TheElesty/electronic-chess/manufacturing/printing/raw/pieces/knight.stl

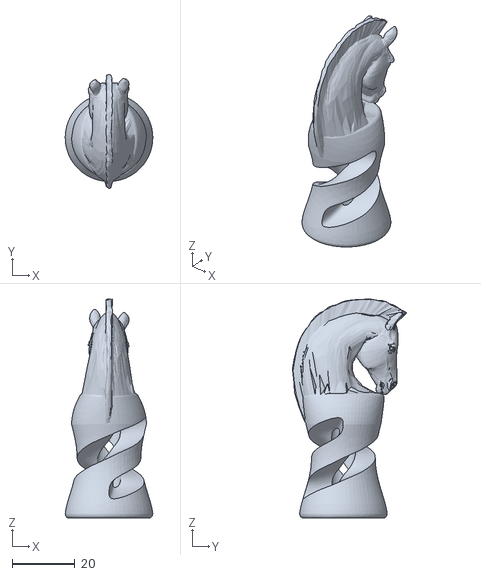
[picture p15: CAD file, 2024-05-08]
manufacturing/printing/raw/pieces/knight.stl
28.0 x 36.5 x 70.0
