TheElesty/electronic-chess/board_model/MODELS/Assets/_RFID-RC522.cd1ec80f-b667-4655-b6b3-a21b5d1b7a74 v7.3mf

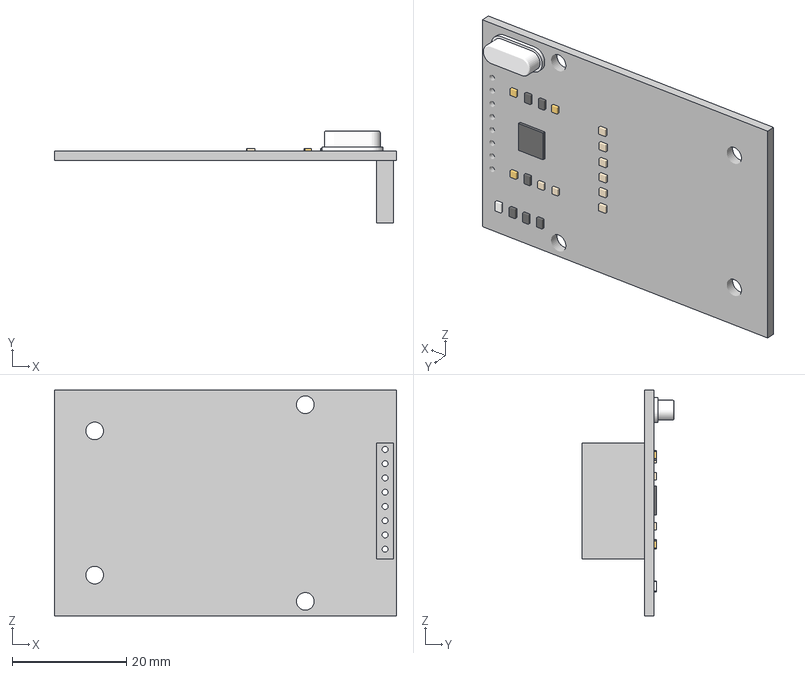
[picture p16: CAD file, 2024-05-08]
board_model/MODELS/Assets/_RFID-RC522.cd1ec80f-b667-4655-b6b3-a21b5d1b7a74 v7.3mf
60.0 x 16.1 x 39.6 mm
Clock
base
