TheElesty/electronic-chess/manufacturing/laser_cut/raw/top_board.dxf

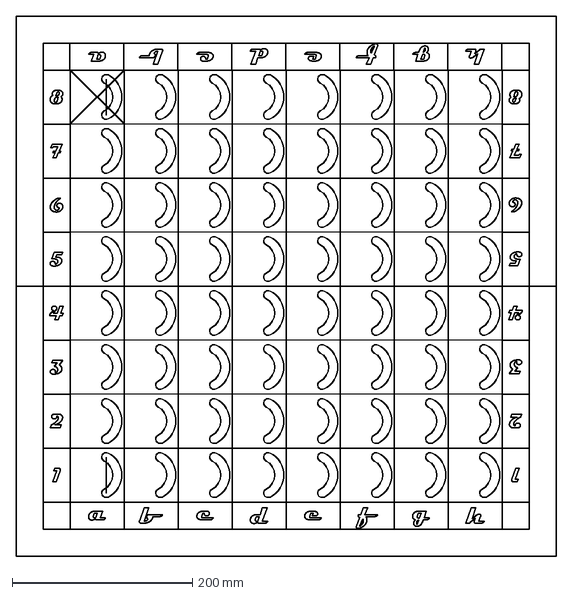
[picture p17: CAD file, 2024-05-08]
manufacturing/laser_cut/raw/top_board.dxf
600.0 x 600.0 mm
