TheElesty/electronic-chess/manufacturing/printing/chess_board_mx_holders.3mf

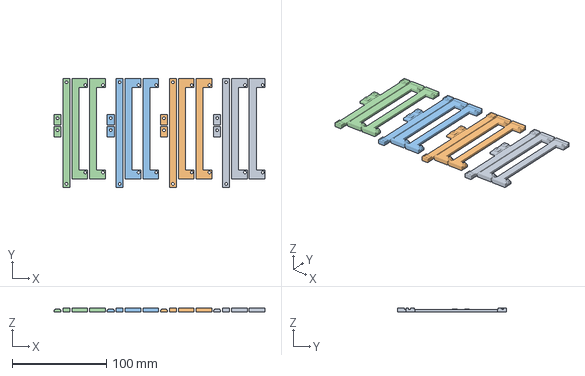
[picture p18: CAD file, 2024-05-08]
manufacturing/printing/chess_board_mx_holders.3mf
224.0 x 115.3 x 4.50 mm
Assembly x 4
