TheElesty/electronic-chess/manufacturing/printing/raw/pieces/rook.stl

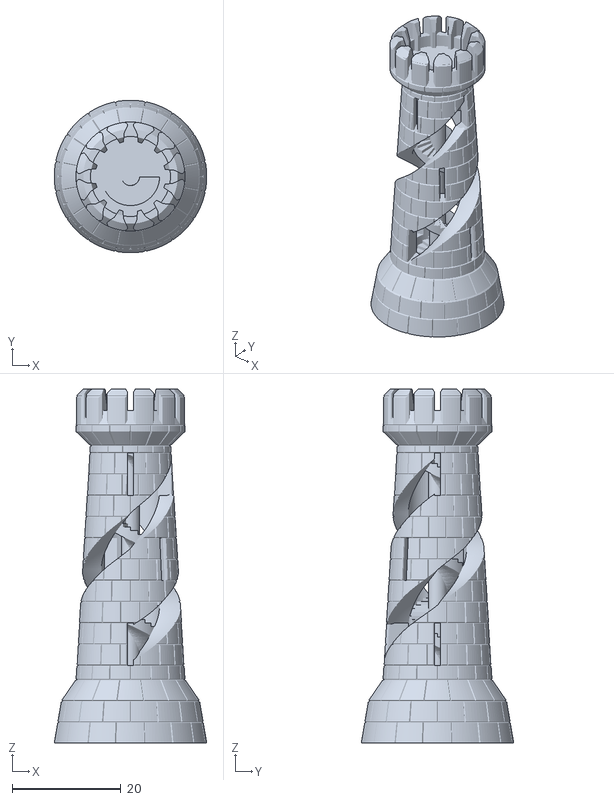
[picture p19: CAD file, 2024-05-08]
manufacturing/printing/raw/pieces/rook.stl
28.0 x 28.0 x 65.0
