TheElesty/electronic-chess/manufacturing/printing/raw/SUPPORTED_light_tunnel.stl

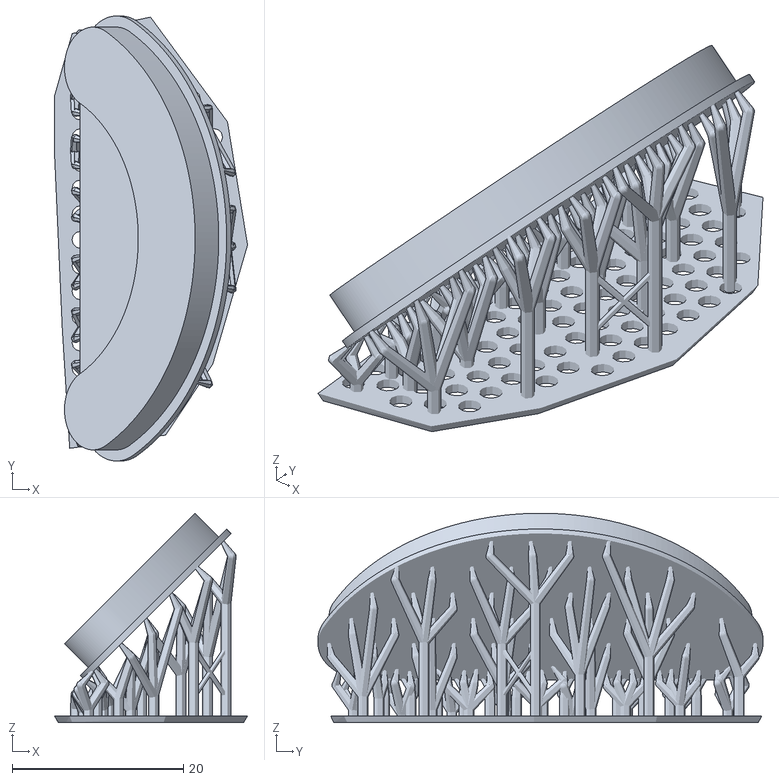
[picture p20: CAD file, 2024-05-08]
manufacturing/printing/raw/SUPPORTED_light_tunnel.stl
22.6 x 52.0 x 24.5
