TheElesty/electronic-chess/manufacturing/laser_cut/raw/short_side.dxf

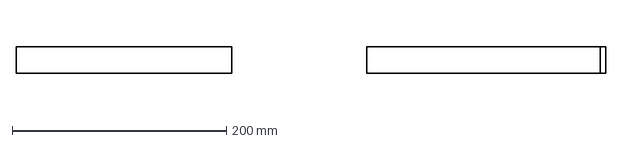
[picture p21: CAD file, 2024-05-08]
manufacturing/laser_cut/raw/short_side.dxf
550.0 x 25.0 mm
