TheElesty/electronic-chess/manufacturing/printing/led_support_2x.3mf

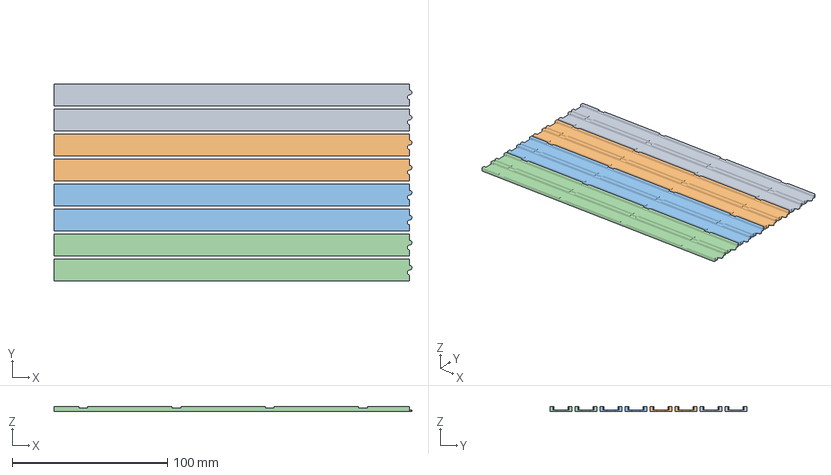
[picture p22: CAD file, 2024-05-08]
manufacturing/printing/led_support_2x.3mf
230.3 x 126.8 x 3.00 mm
Assembly x 4
