TheElesty/electronic-chess/manufacturing/printing/raw/chess_board_mx_holder.stl

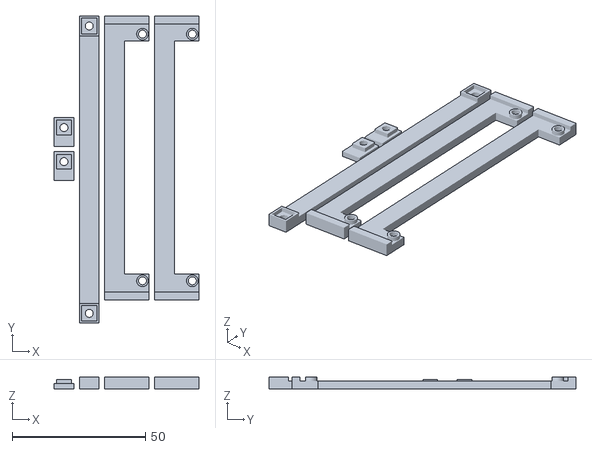
[picture p23: CAD file, 2024-05-08]
manufacturing/printing/raw/chess_board_mx_holder.stl
54.5 x 115.3 x 4.50
