TheElesty/electronic-chess/manufacturing/printing/raw/pieces/king.stl

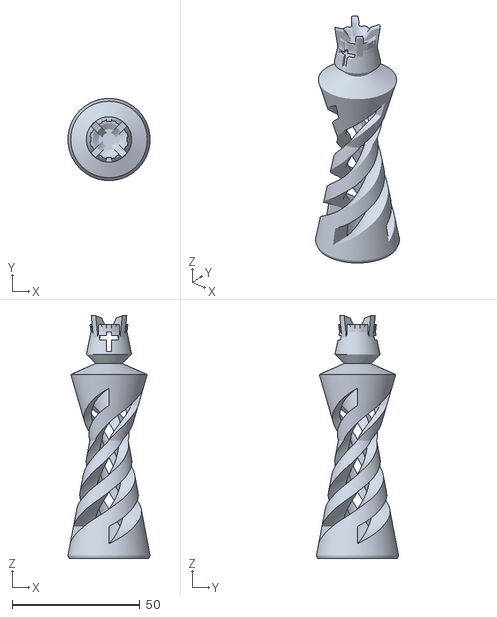
[picture p24: CAD file, 2024-05-08]
manufacturing/printing/raw/pieces/king.stl
32.1 x 32.1 x 95.0
