TheElesty/electronic-chess/manufacturing/laser_cut/raw/foam.dxf

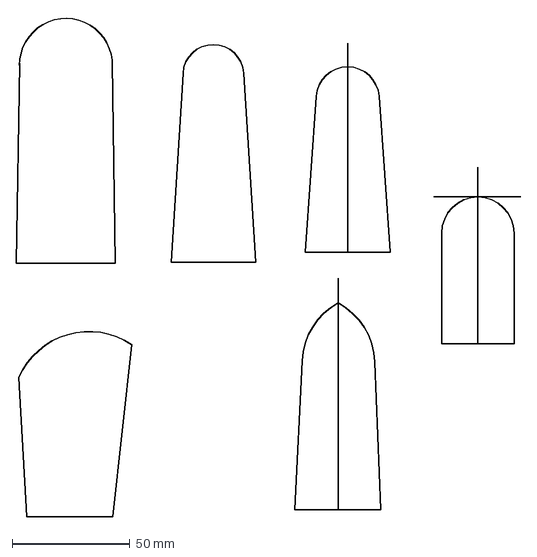
[picture p25: CAD file, 2024-05-08]
manufacturing/laser_cut/raw/foam.dxf
214.4 x 212.9 mm
