TheElesty/electronic-chess/manufacturing/printing/chess_board_sides.3mf

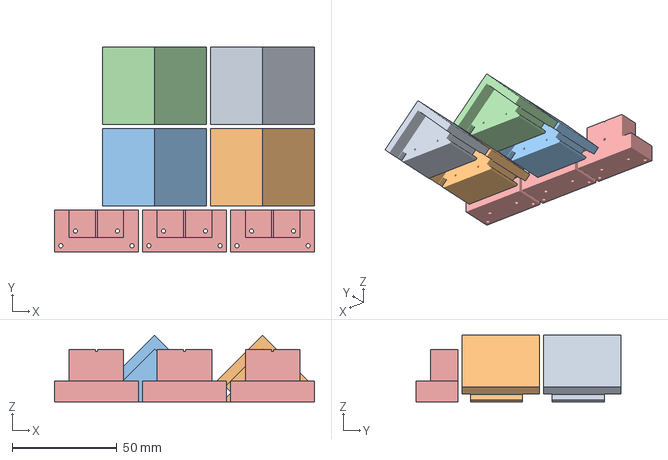
[picture p26: CAD file, 2024-05-08]
manufacturing/printing/chess_board_sides.3mf
124.0 x 97.8 x 31.8 mm
corner_stand x 4
Assembly
