TheElesty/electronic-chess/manufacturing/printing/raw/led_support.stl

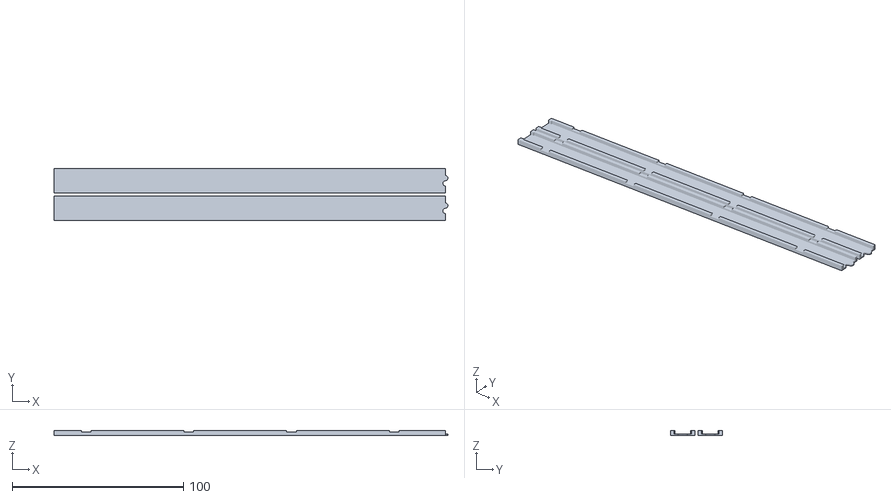
[picture p27: CAD file, 2024-05-08]
manufacturing/printing/raw/led_support.stl
230.3 x 30.2 x 3.00
