TheElesty/electronic-chess/manufacturing/printing/led_solderRig.3mf

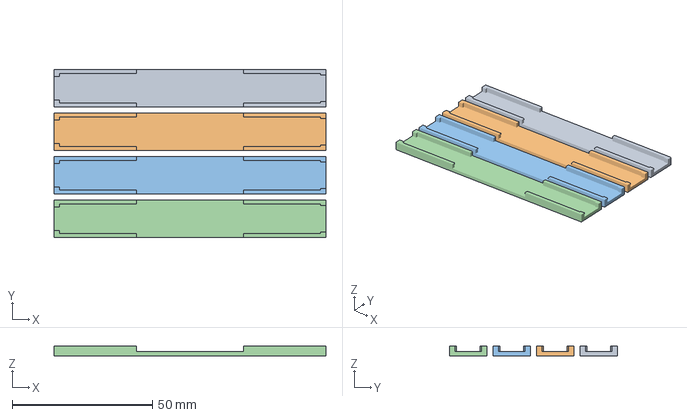
[picture p28: CAD file, 2024-05-08]
manufacturing/printing/led_solderRig.3mf
97.0 x 60.0 x 3.50 mm
