TheElesty/electronic-chess/manufacturing/printing/raw/chess_board_side_support.stl

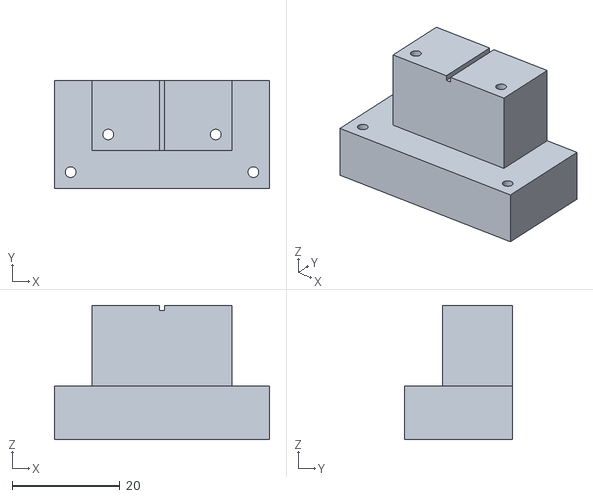
[picture p29: CAD file, 2024-05-08]
manufacturing/printing/raw/chess_board_side_support.stl
40.0 x 20.0 x 25.0
