TheElesty/electronic-chess/manufacturing/printing/chess_clock.3mf

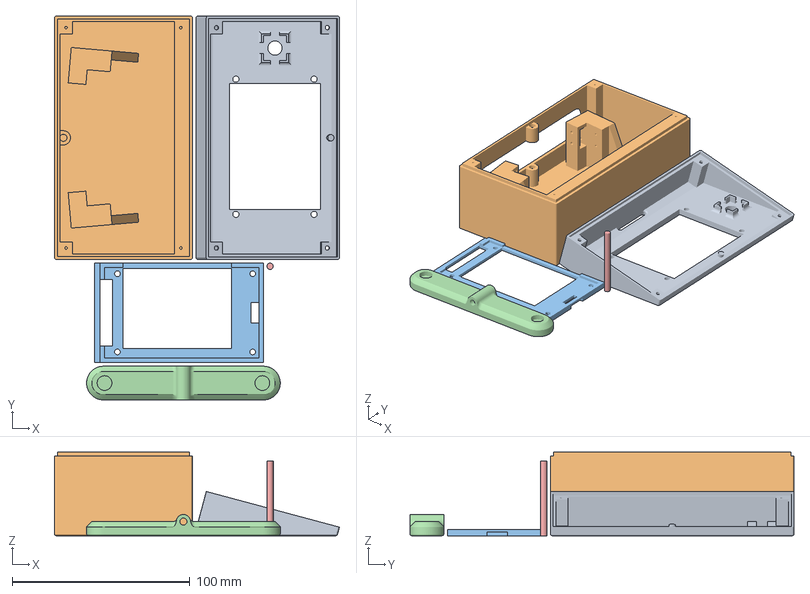
[picture p30: CAD file, 2024-05-08]
manufacturing/printing/chess_clock.3mf
160.3 x 216.0 x 47.0 mm
Front_panel
back_panel
tft_backplate
paddle
hinge
