TheElesty/electronic-chess/manufacturing/printing/raw/chess_board_corner.stl

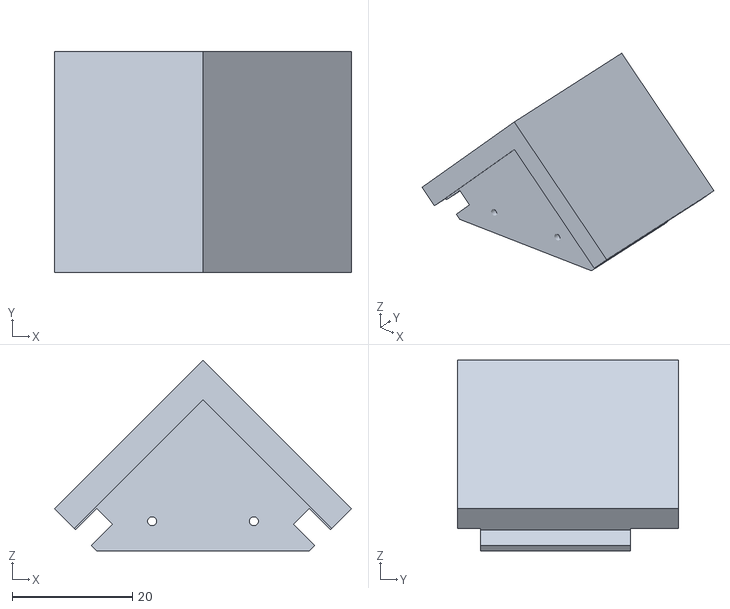
[picture p31: CAD file, 2024-05-08]
manufacturing/printing/raw/chess_board_corner.stl
49.5 x 36.9 x 31.8
