TheElesty/electronic-chess/manufacturing/printing/raw/chess_clock_front.stl

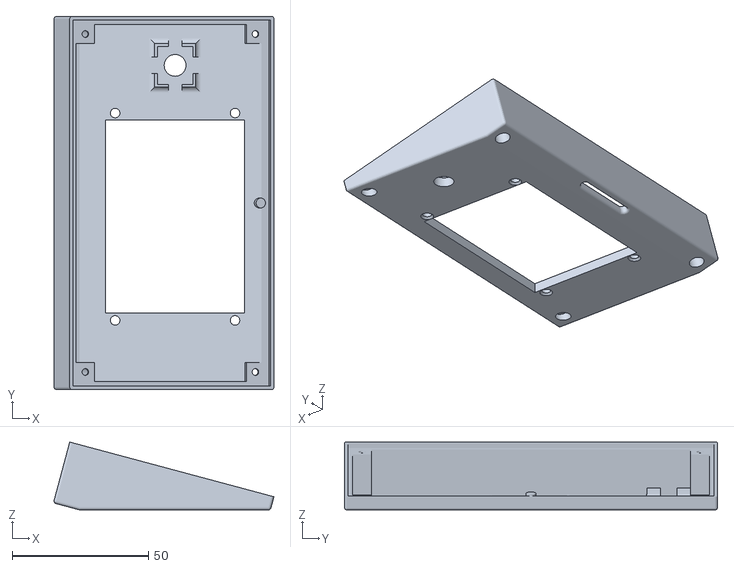
[picture p32: CAD file, 2024-05-08]
manufacturing/printing/raw/chess_clock_front.stl
80.7 x 137.0 x 24.9
