TheElesty/electronic-chess/manufacturing/printing/raw/led_solderRig v2.stl

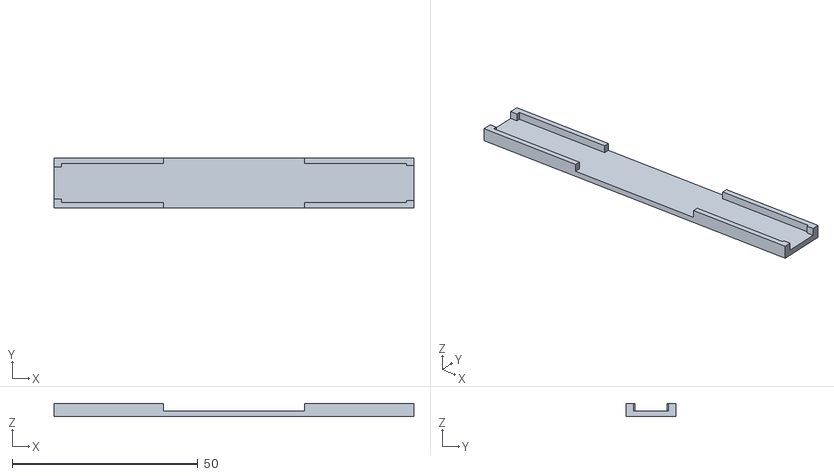
[picture p33: CAD file, 2024-05-08]
manufacturing/printing/raw/led_solderRig v2.stl
97.0 x 13.5 x 3.50
