TheElesty/electronic-chess/manufacturing/printing/raw/chess_board_led_holder.stl

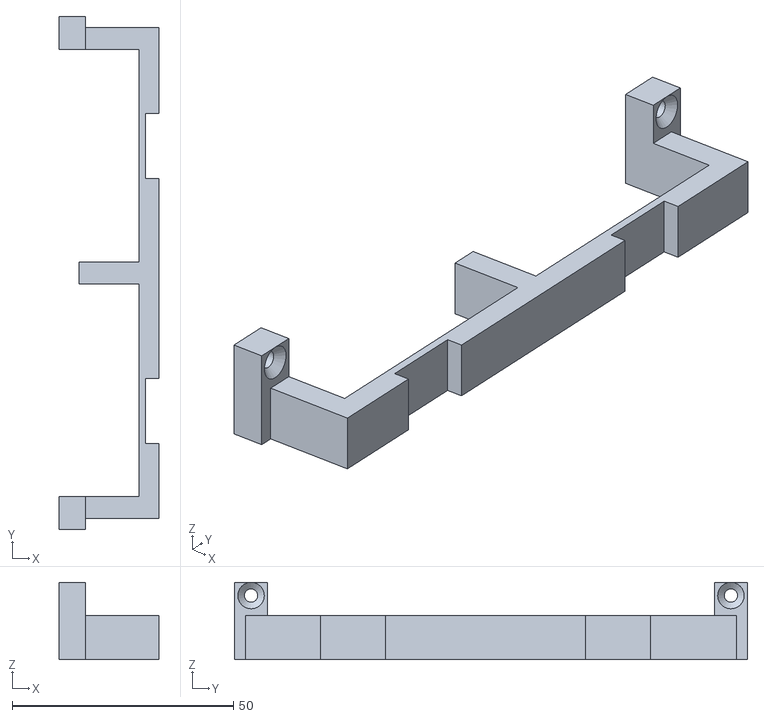
[picture p34: CAD file, 2024-05-08]
manufacturing/printing/raw/chess_board_led_holder.stl
22.6 x 116.0 x 17.5
