TheElesty/electronic-chess/manufacturing/printing/raw/chess_clock_back.stl

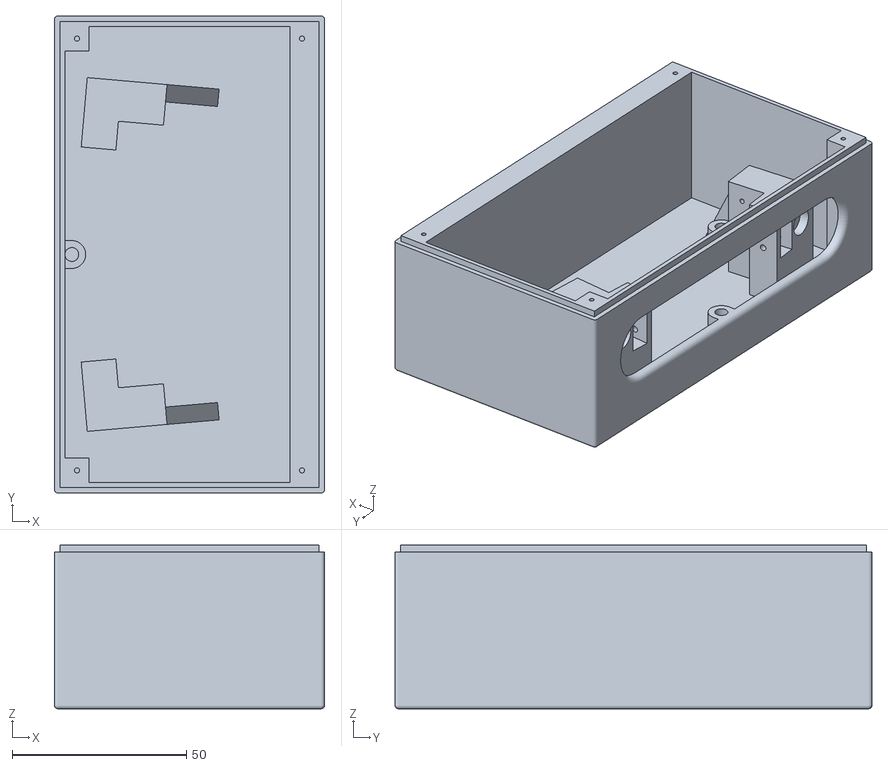
[picture p35: CAD file, 2024-05-08]
manufacturing/printing/raw/chess_clock_back.stl
77.6 x 137.0 x 47.0
