TheElesty/electronic-chess/manufacturing/printing/raw/chess_clock_lcd_backplate.stl

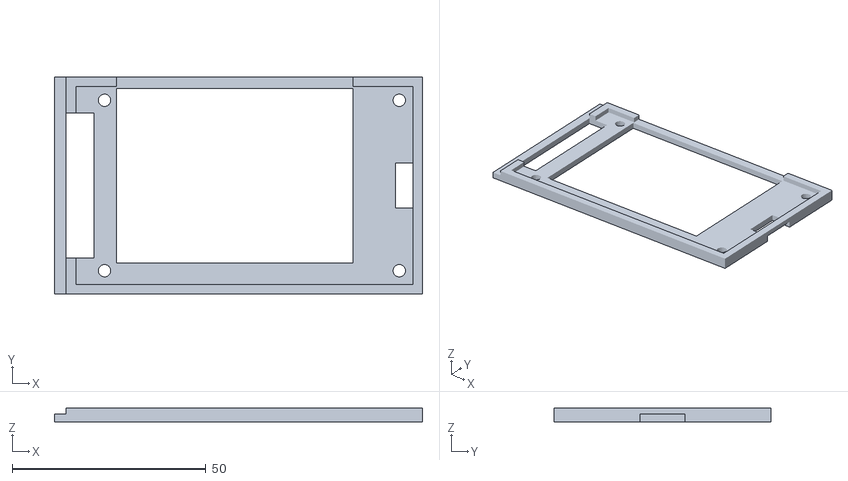
[picture p36: CAD file, 2024-05-08]
manufacturing/printing/raw/chess_clock_lcd_backplate.stl
95.0 x 56.0 x 3.60
