TheElesty/electronic-chess/manufacturing/printing/raw/chess_clock_pin.stl

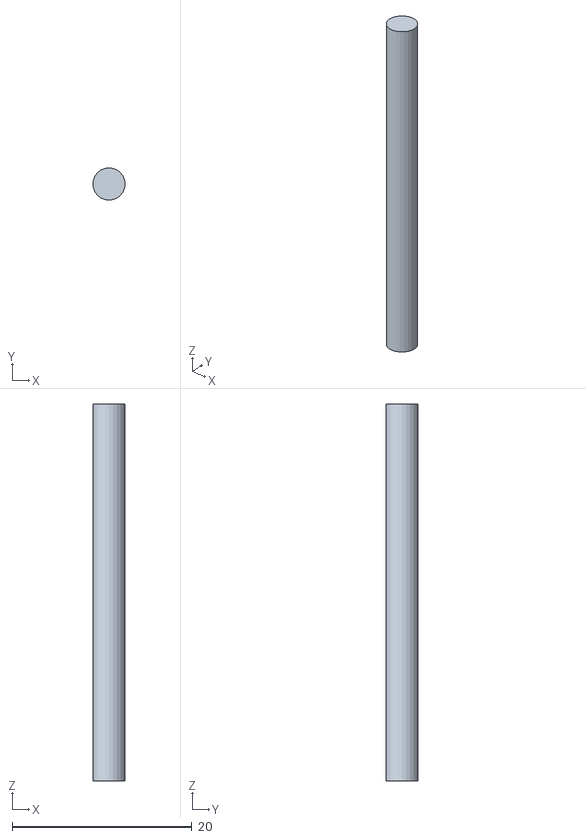
[picture p37: CAD file, 2024-05-08]
manufacturing/printing/raw/chess_clock_pin.stl
3.60 x 3.60 x 42.0
